TjarkG/RPM411/RawScans/1_FrontPopulated/IMG_4745.jpg

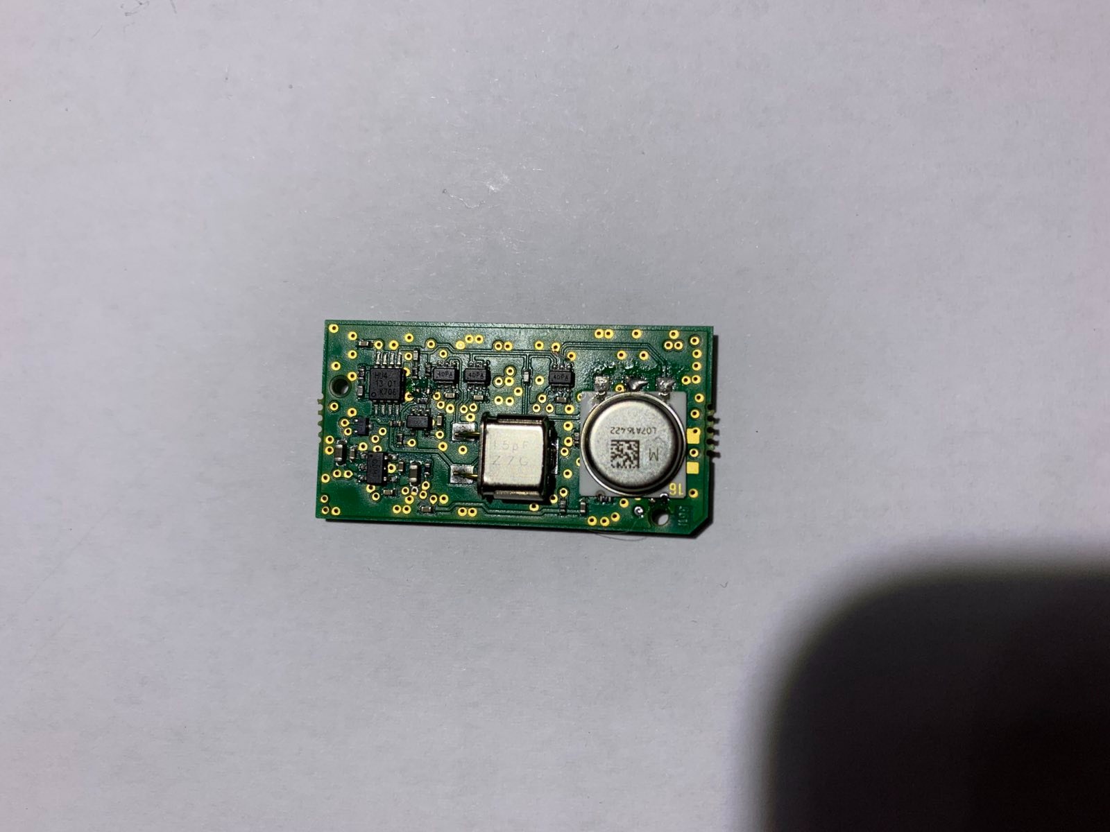
RawScans/1_FrontPopulated/IMG_4745.jpg
