TjarkG/RPM411/RawScans/1_FrontPopulated/Scanned-image_20-07-2022-185520-2.jpg

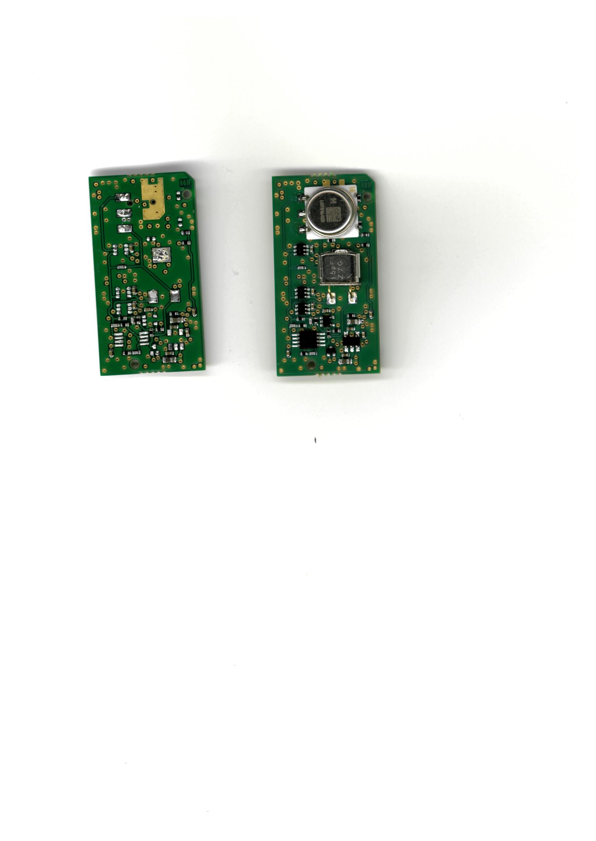
RawScans/1_FrontPopulated/Scanned-image_20-07-2022-185520-2.jpg
