TjarkG/RPM411/RawScans/1_FrontPopulated/signal-2022-07-20-200623_023.jpeg

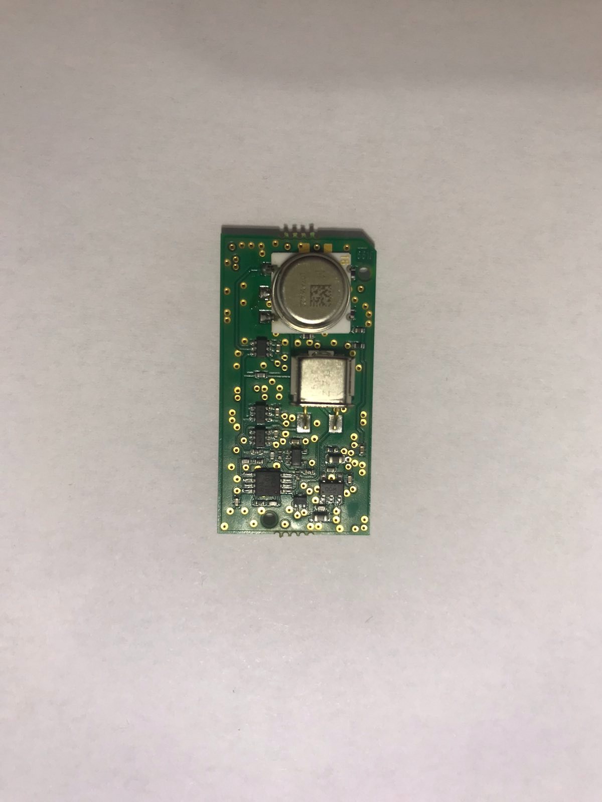
RawScans/1_FrontPopulated/signal-2022-07-20-200623_023.jpeg
