TjarkG/RPM411/RawScans/1_FrontPopulated/signal-2022-07-20-200710_004.jpeg

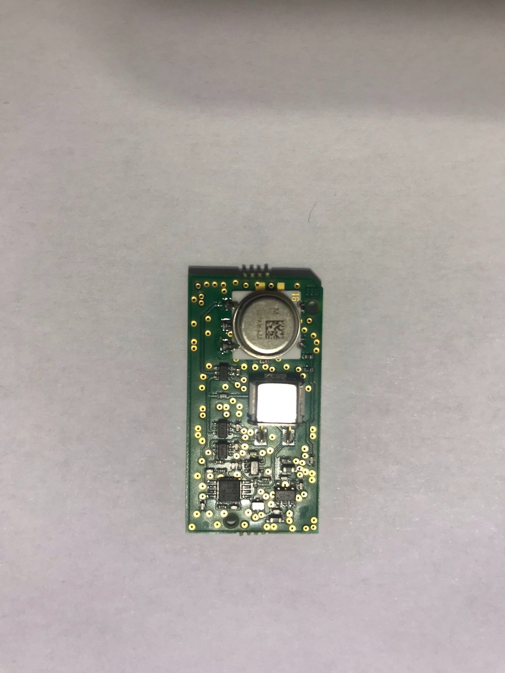
RawScans/1_FrontPopulated/signal-2022-07-20-200710_004.jpeg
