TjarkG/RPM411/RawScans/1_FrontPopulated/signal-2022-07-20-200710_014.jpeg

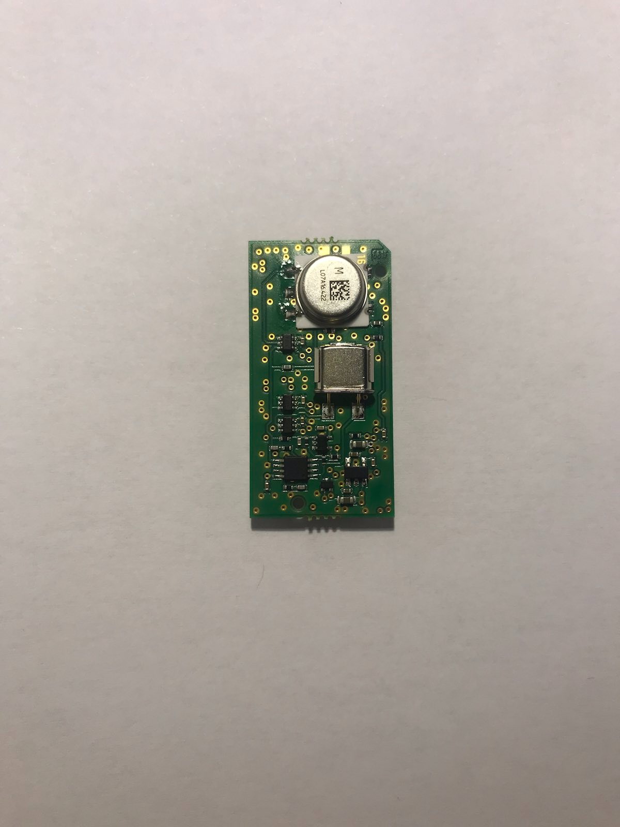
RawScans/1_FrontPopulated/signal-2022-07-20-200710_014.jpeg
