TjarkG/RPM411/RawScans/2_FrontSMDs/Scanned-image_20-07-2022-185831-1.jpg

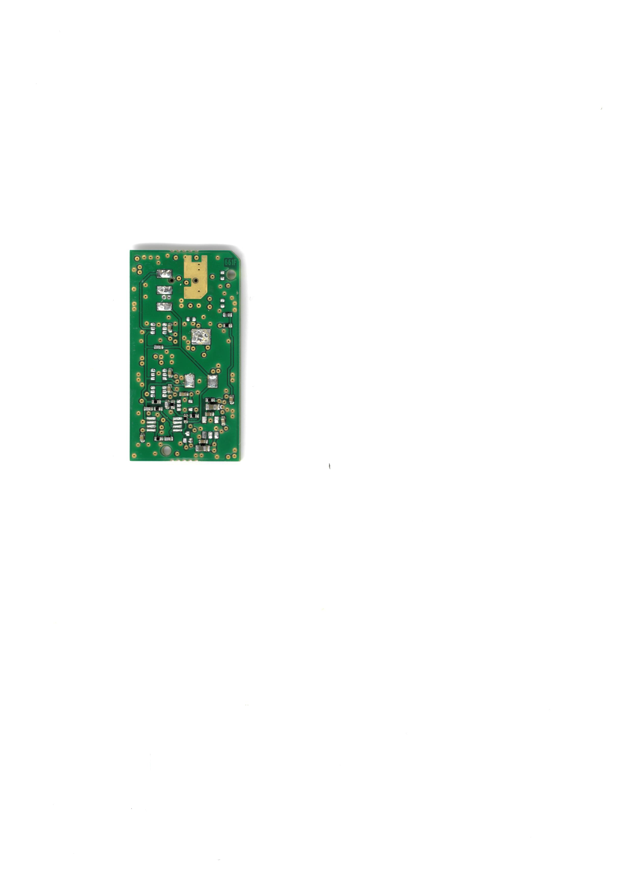
RawScans/2_FrontSMDs/Scanned-image_20-07-2022-185831-1.jpg
