TjarkG/RPM411/RawScans/2_FrontSMDs/signal-2022-07-20-200710_001.jpeg

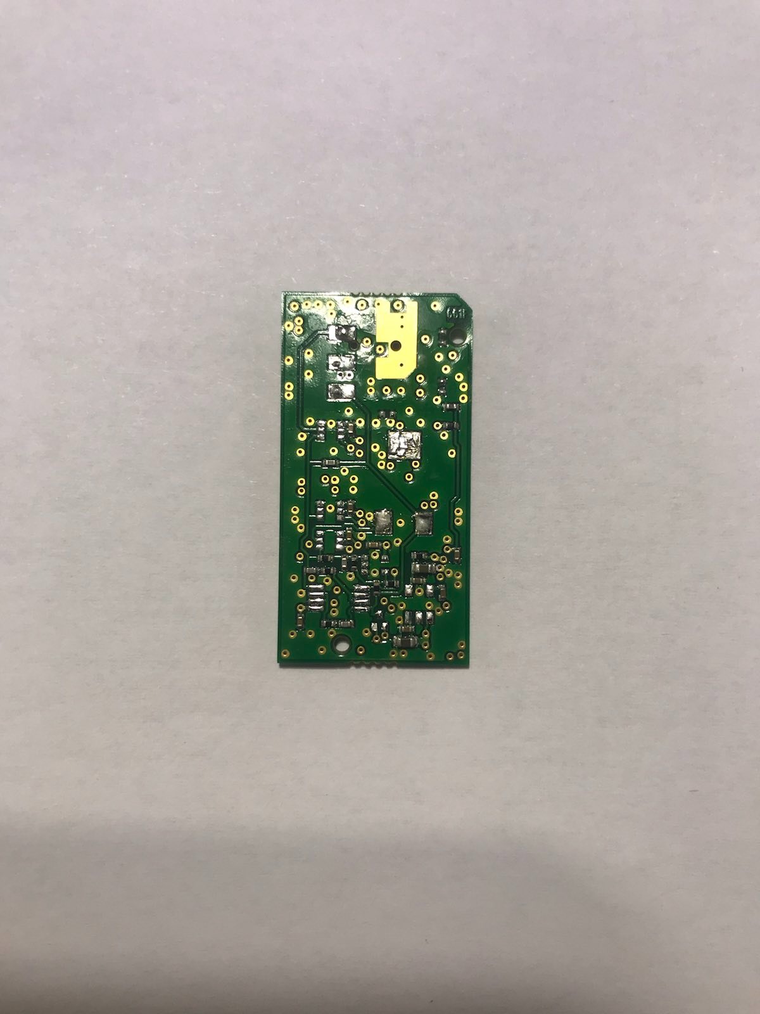
RawScans/2_FrontSMDs/signal-2022-07-20-200710_001.jpeg
