TjarkG/RPM411/RawScans/7_BackSMDs/Scanned-image_20-07-2022-185831-2.jpg

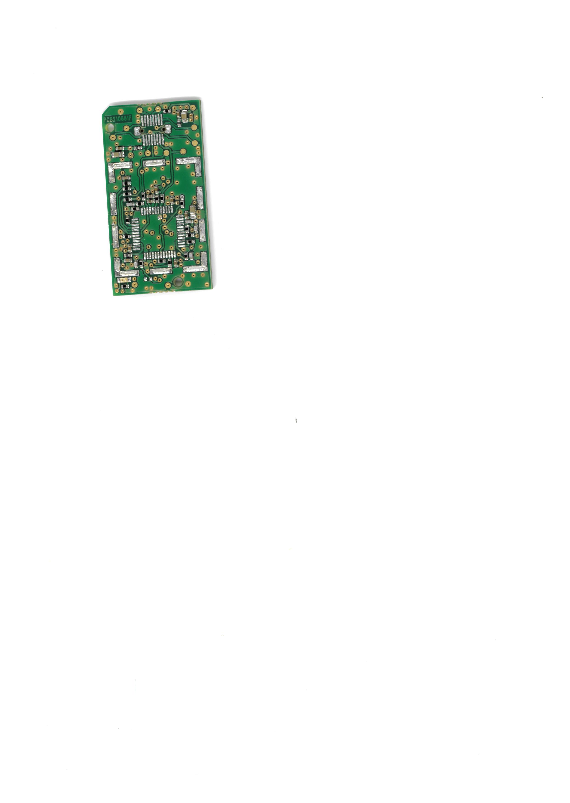
RawScans/7_BackSMDs/Scanned-image_20-07-2022-185831-2.jpg
