TjarkG/RPM411/RawScans/7_BackSMDs/signal-2022-07-20-200710_003.jpeg

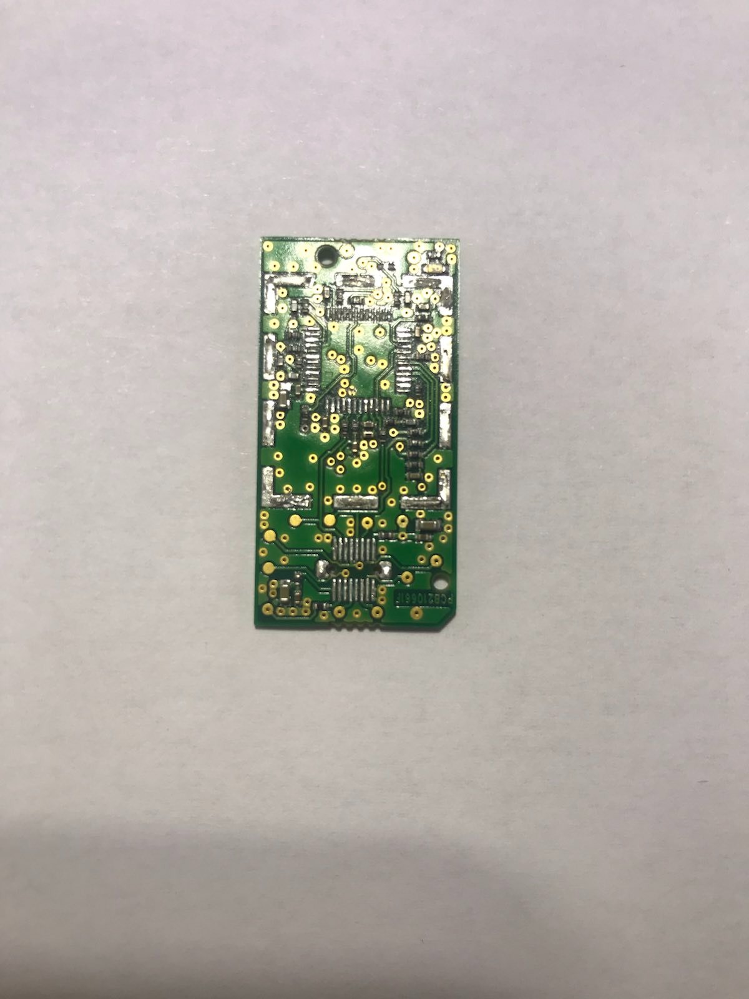
RawScans/7_BackSMDs/signal-2022-07-20-200710_003.jpeg
