TjarkG/RPM411/RawScans/8_BackPopulated/signal-2022-07-20-200623_013.jpeg

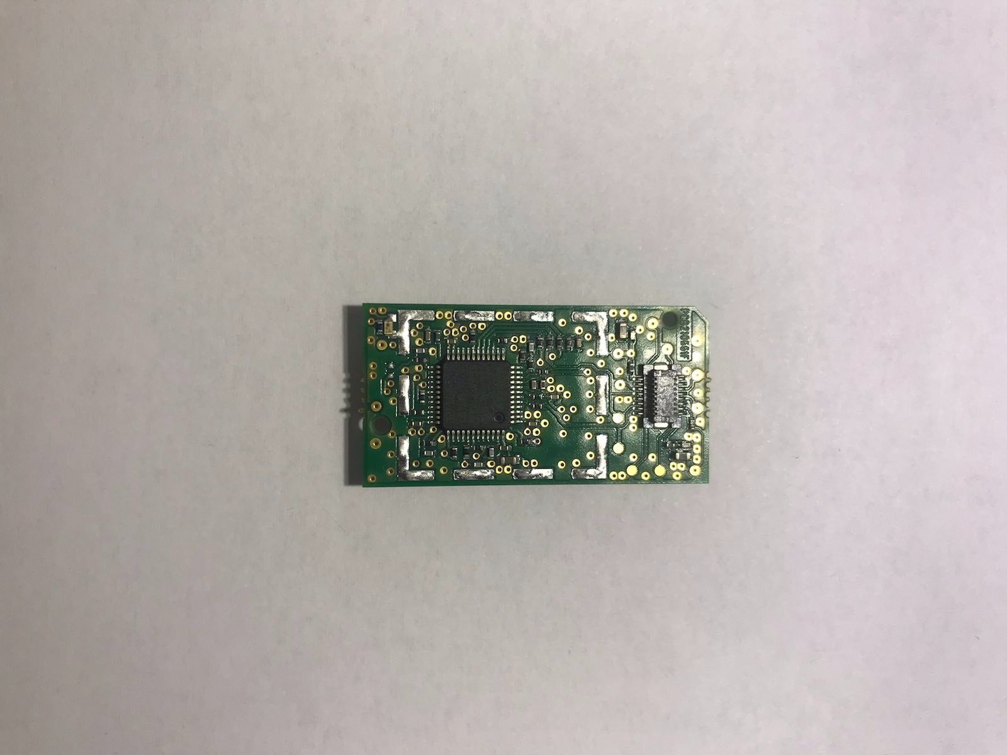
RawScans/8_BackPopulated/signal-2022-07-20-200623_013.jpeg
