TjarkG/RPM411/RawScans/9_BackShield/signal-2022-07-20-200623_002.jpeg

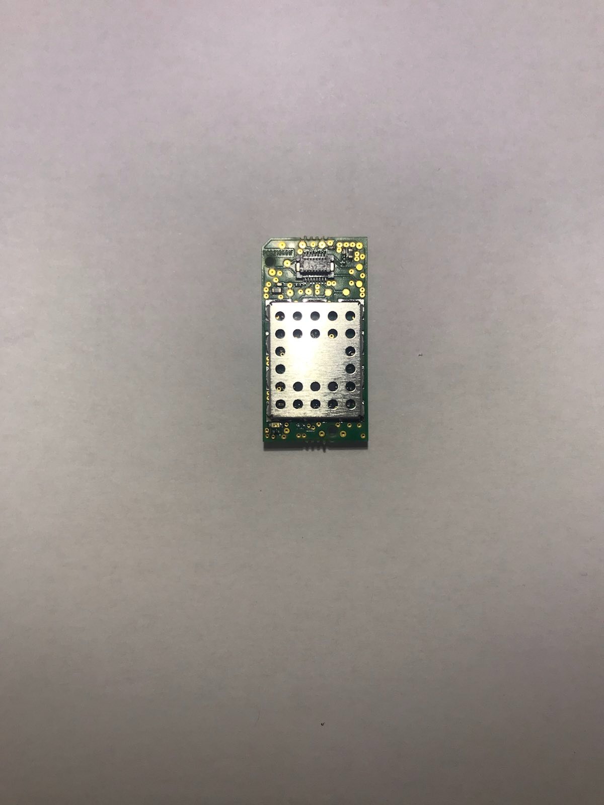
RawScans/9_BackShield/signal-2022-07-20-200623_002.jpeg
