TjarkG/RPM411/RawScans/9_BackShield/signal-2022-07-20-200623_004.jpeg

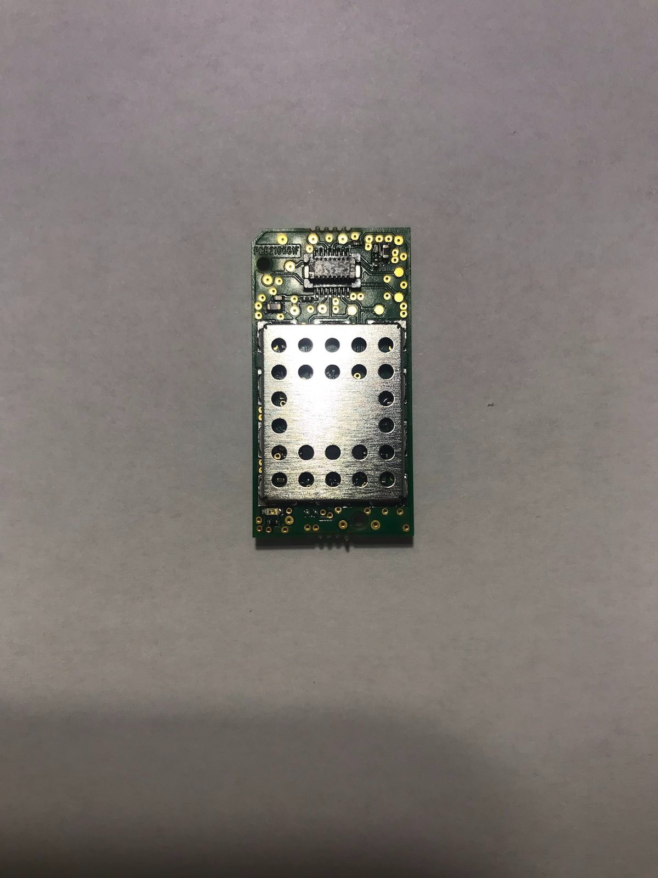
RawScans/9_BackShield/signal-2022-07-20-200623_004.jpeg
