TjarkG/RPM411/RawScans/10_BackSticke/signal-2022-07-20-200710_010.jpeg

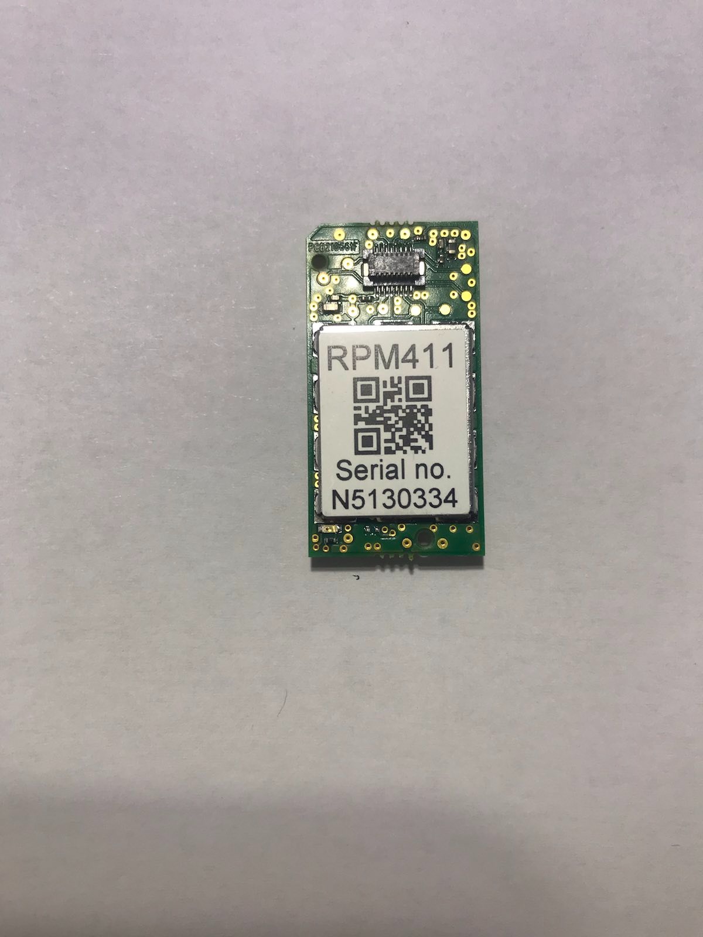
RawScans/10_BackSticke/signal-2022-07-20-200710_010.jpeg
