TjarkG/RPM411/RawScans/CombiScans/1/Scanned-image_20-07-2022-212549-1.jpg

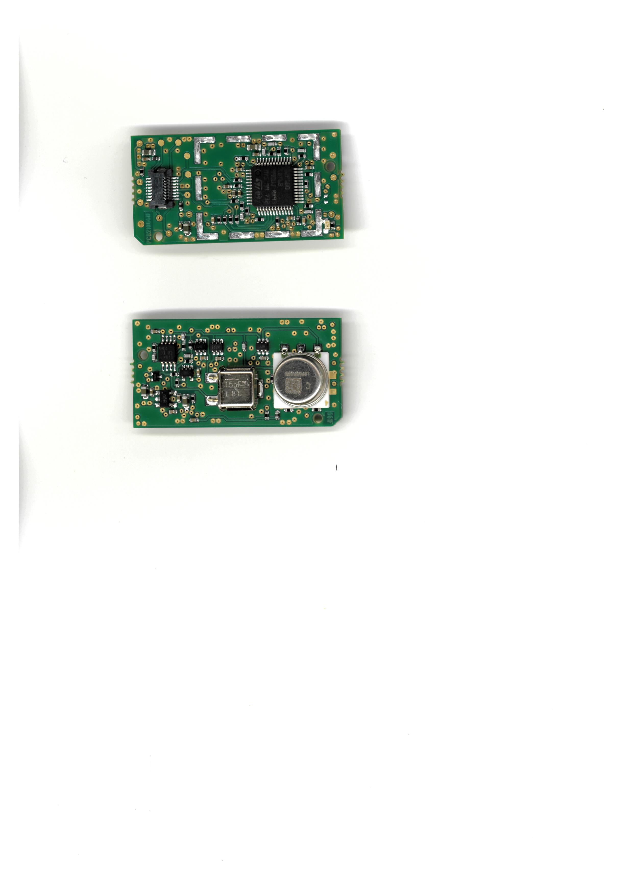
RawScans/CombiScans/1/Scanned-image_20-07-2022-212549-1.jpg
