TjarkG/RPM411/RawScans/CombiScans/2/Scanned-image_20-07-2022-213727-1.jpg

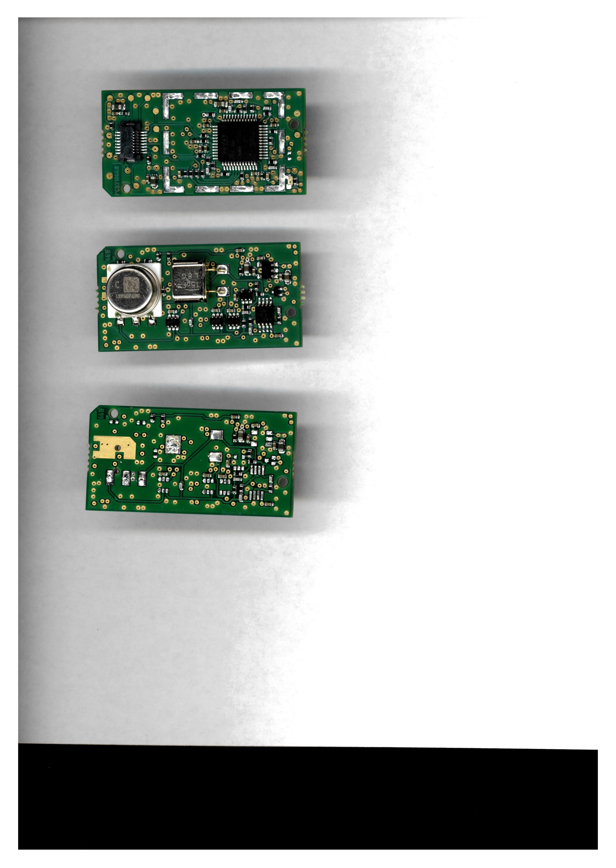
RawScans/CombiScans/2/Scanned-image_20-07-2022-213727-1.jpg
