TjarkG/RPM411/RawScans/Shield/signal-2022-07-20-200623_006.jpeg

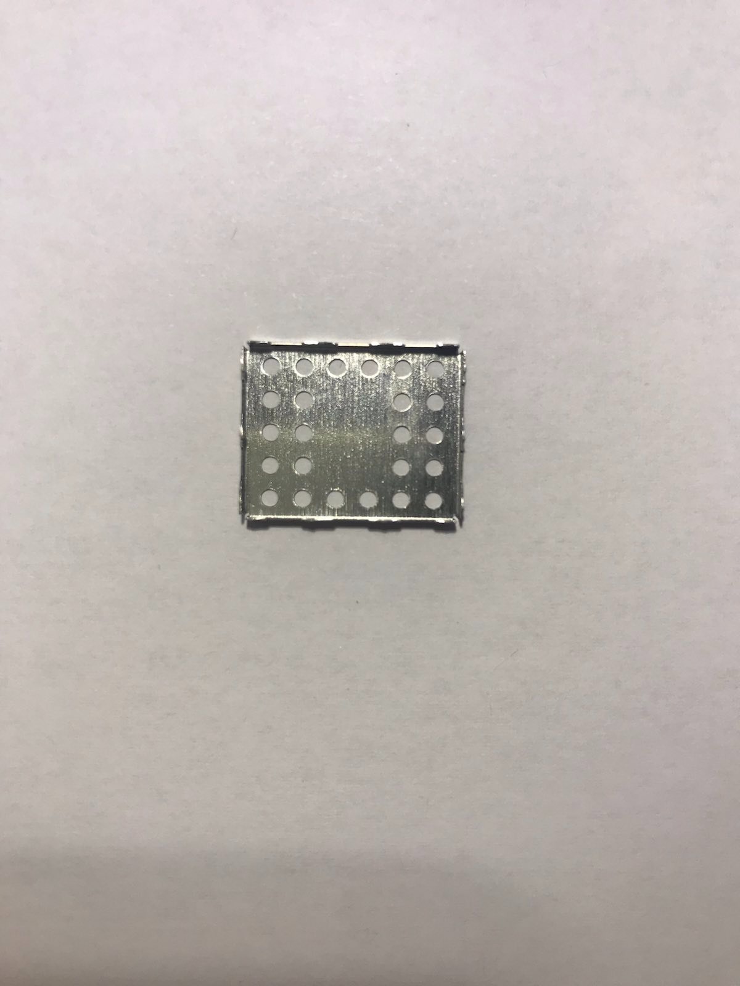
RawScans/Shield/signal-2022-07-20-200623_006.jpeg
